zhol0777/minilabaen/minibaen r2.kicad_sch

## KiCad design minibaen r2.kicad_sch (2024-08-04)

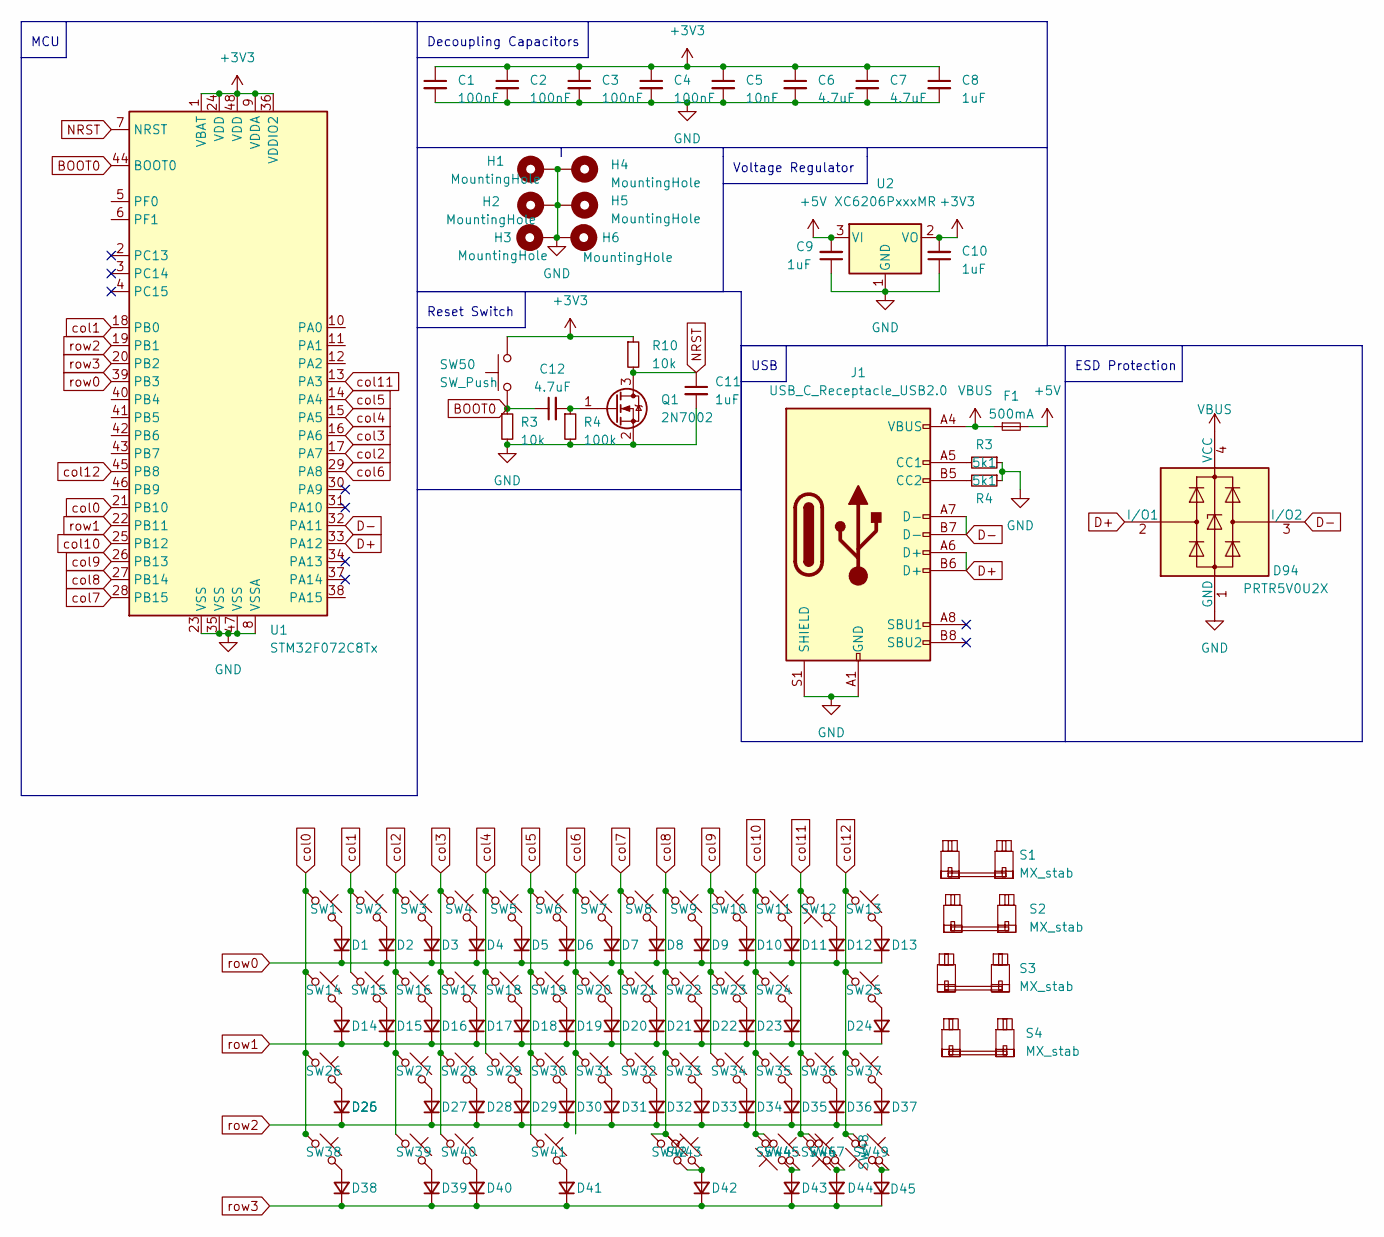
[picture p5: schematic minibaen r2.kicad_sch]

Parts:
C1, C2, C3, C4: 100nF; C_0402_1005Metric
C5: 10nF; C_0402_1005Metric
C6, C7, C12: 4.7uF; C_0402_1005Metric
C8, C9, C10, C11: 1uF; C_0402_1005Metric
D1, D2, D3, D4, D5, D6, D7, D8, D9, D10, D11, D12, D13, D14, D15, D16, D17, D18, D19, D20, D21, D22, D23, D24, D25, D26, D27, D28, D29, D30, D31, D32, D33, D34, D35, D36, D37, D38, D39, D40, D41, D42, D43, D44, D45: D_Small; D_SOD-123
D94: PRTR5V0U2X; SOT-143
F1: 500mA; Fuse_0603_1608Metric
H1, H2, H3, H4, H5, H6: MountingHole; MountingHole_2.2mm_M2_DIN965_Pad
J1: USB_C_Receptacle_USB2.0; USB_C_Receptacle_HRO_TYPE-C-31-M-12
Q1: 2N7002; SOT-23
R3, R10: 10k; R_0402_1005Metric
R4: 100k; R_0402_1005Metric
S1: MX_stab; STAB_MX_2.75u
S2: MX_stab; STAB_MX_3u
S3: MX_stab; STAB_MX_2u
S4: MX_stab; STAB_MX_6.25u
SW1, SW2, SW3, SW4, SW5, SW6, SW7, SW8, SW9, SW10, SW11, SW12, SW13, SW15, SW16, SW17, SW18, SW19, SW20, SW21, SW22, SW23, SW24, SW27, SW28, SW29, SW30, SW31, SW32, SW33, SW34, SW35, SW36, SW37, SW39, SW41, SW42, SW43, SW45, SW46, SW47, SW49: MX_SW_solder; SW_MX_1u
SW14, SW38, SW40, SW44, SW48: MX_SW_solder; SW_MX_1.25u
SW25, SW26: MX_SW_solder; SW_MX_1.75u
SW50: SW_Push; SW_SPST_TL3342
U1: STM32F072C8Tx; LQFP-48_7x7mm_P0.5mm
U2: XC6206PxxxMR; SOT-23

Connections:
+3V3: C1.1, C2.1, C3.1, C4.1, C5.1, C6.1, C7.1, C8.1, C10.2, R10.1, SW50.2, U1.1 (VBAT), U1.9 (VDDA), U1.24 (VDD), U1.36 (VDDIO2), U1.48 (VDD), U2.2 (VO)
+5V: C9.2, F1.2, U2.3 (VI)
BOOT0: C12.1, R3.1, SW50.1, U1.44 (BOOT0)
D+: D94.2 (I/O1), J1.A6 (D+), J1.B6 (D+), U1.33 (PA12)
D-: D94.3 (I/O2), J1.A7 (D-), J1.B7 (D-), U1.32 (PA11)
GND: C1.2, C2.2, C3.2, C4.2, C5.2, C6.2, C7.2, C8.2, C9.1, C10.1, C11.2, D94.1 (GND), H1.1, H2.1, H3.1, H4.1, H5.1, H6.1, J1.A1 (GND), J1.A12 (GND), J1.B1 (GND), J1.B12 (GND), J1.S1 (SHIELD), Q1.2 (S), R3.1, R3.2, R4.1, R4.2, U1.8 (VSSA), U1.23 (VSS), U1.35 (VSS), U1.47 (VSS), U2.1 (GND)
NRST: C11.1, Q1.3 (D), R10.2, U1.7 (NRST)
unnamed: C12.2, Q1.1 (G), R4.1
unnamed: D1.2 (A), SW1.2
unnamed: D2.2 (A), SW2.2
unnamed: D3.2 (A), SW3.2
unnamed: D4.2 (A), SW4.2
unnamed: D5.2 (A), SW5.2
unnamed: D6.2 (A), SW6.2
unnamed: D7.2 (A), SW7.2
unnamed: D8.2 (A), SW8.2
unnamed: D9.2 (A), SW9.2
unnamed: D10.2 (A), SW10.2
unnamed: D11.2 (A), SW11.2
unnamed: D12.2 (A), SW12.1
unnamed: D13.2 (A), SW13.2
unnamed: D14.2 (A), SW14.2
unnamed: D15.2 (A), SW15.2
unnamed: D16.2 (A), SW16.2
unnamed: D17.2 (A), SW17.2
unnamed: D18.2 (A), SW18.2
unnamed: D19.2 (A), SW19.2
unnamed: D20.2 (A), SW20.2
unnamed: D21.2 (A), SW21.2
unnamed: D22.2 (A), SW22.2
unnamed: D23.2 (A), SW23.2
unnamed: D24.2 (A), SW24.2
unnamed: D25.2 (A), SW25.2
unnamed: D26.2 (A), SW26.2
unnamed: D27.2 (A), SW27.2
unnamed: D28.2 (A), SW28.2
unnamed: D29.2 (A), SW29.2
unnamed: D30.2 (A), SW30.2
unnamed: D31.2 (A), SW31.2
unnamed: D32.2 (A), SW32.2
unnamed: D33.2 (A), SW33.2
unnamed: D34.2 (A), SW34.2
unnamed: D35.2 (A), SW35.2
unnamed: D36.2 (A), SW36.2
unnamed: D37.2 (A), SW37.2
unnamed: D38.2 (A), SW38.2
unnamed: D39.2 (A), SW39.2
unnamed: D40.2 (A), SW40.2
unnamed: D41.2 (A), SW41.2
unnamed: D42.2 (A), SW42.2, SW43.2
unnamed: D43.2 (A), SW44.1, SW45.2
unnamed: D44.2 (A), SW46.2, SW47.1
unnamed: D45.2 (A), SW48.2, SW49.2
unnamed: J1.A5 (CC1), R3.2
unnamed: J1.B5 (CC2), R4.2
VBUS: D94.4 (VCC), F1.1, J1.A4 (VBUS), J1.A9 (VBUS), J1.B4 (VBUS), J1.B9 (VBUS)
col0: SW1.1, SW14.1, SW26.1, SW38.1, U1.21 (PB10)
col1: SW2.1, SW15.1, U1.18 (PB0)
col2: SW3.1, SW16.1, SW27.1, SW39.1, U1.17 (PA7)
col3: SW4.1, SW17.1, SW28.1, SW40.1, U1.16 (PA6)
col4: SW5.1, SW18.1, SW29.1, U1.15 (PA5)
col5: SW6.1, SW19.1, SW30.1, SW41.1, U1.14 (PA4)
col6: SW7.1, SW20.1, SW31.1, U1.29 (PA8)
col7: SW8.1, SW21.1, SW32.1, U1.28 (PB15)
col8: SW9.1, SW22.1, SW33.1, SW42.1, SW43.1, U1.27 (PB14)
col9: SW10.1, SW23.1, SW34.1, U1.26 (PB13)
col10: SW11.1, SW24.1, SW35.1, SW44.2, SW45.1, U1.25 (PB12)
col11: SW12.2, SW36.1, SW46.1, SW47.2, U1.13 (PA3)
col12: SW13.1, SW25.1, SW37.1, SW48.1, SW49.1, U1.45 (PB8)
row0: D1.1 (K), D2.1 (K), D3.1 (K), D4.1 (K), D5.1 (K), D6.1 (K), D7.1 (K), D8.1 (K), D9.1 (K), D10.1 (K), D11.1 (K), D12.1 (K), D13.1 (K), U1.39 (PB3)
row1: D14.1 (K), D15.1 (K), D16.1 (K), D17.1 (K), D18.1 (K), D19.1 (K), D20.1 (K), D21.1 (K), D22.1 (K), D23.1 (K), D24.1 (K), D25.1 (K), U1.22 (PB11)
row2: D26.1 (K), D27.1 (K), D28.1 (K), D29.1 (K), D30.1 (K), D31.1 (K), D32.1 (K), D33.1 (K), D34.1 (K), D35.1 (K), D36.1 (K), D37.1 (K), U1.19 (PB1)
row3: D38.1 (K), D39.1 (K), D40.1 (K), D41.1 (K), D42.1 (K), D43.1 (K), D44.1 (K), D45.1 (K), U1.20 (PB2)

Notes on the sheet:
Voltage Regulator
ESD Protection
Decoupling Capacitors
USB
Reset Switch
MCU
